profdc9/RFBitBanger/BitBangDisplay/BitBangDisplay-Bottom.png

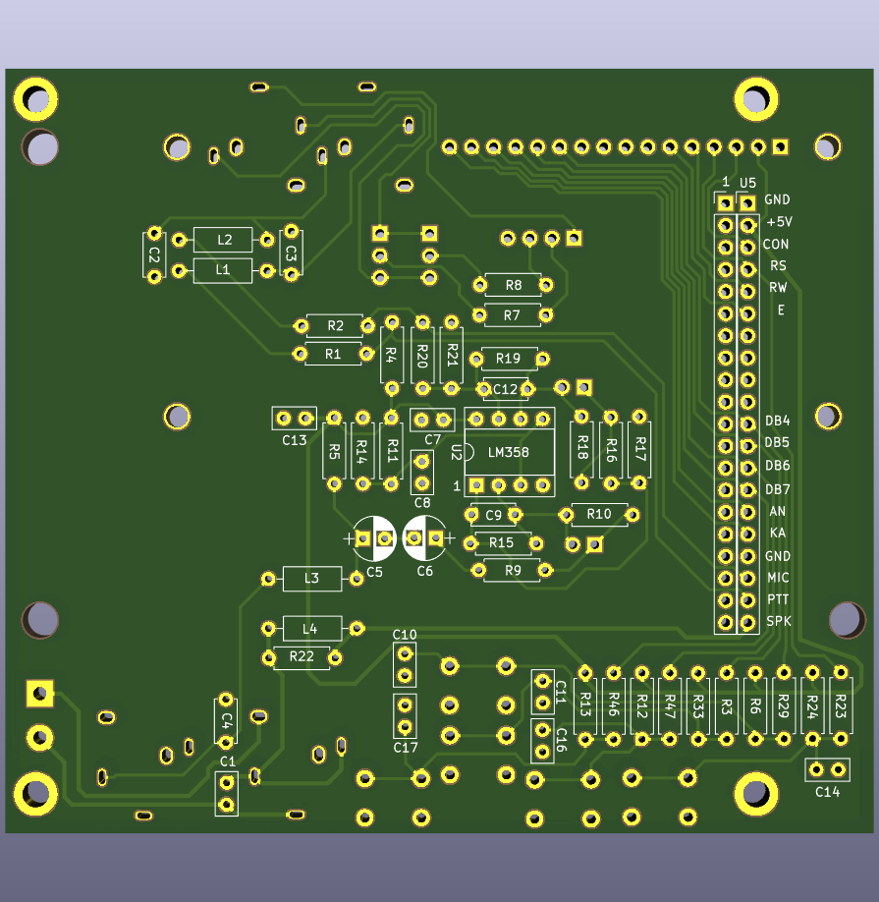
BitBangDisplay/BitBangDisplay-Bottom.png
