profdc9/RFBitBanger/PortableTerminal/PortableTerminal.png

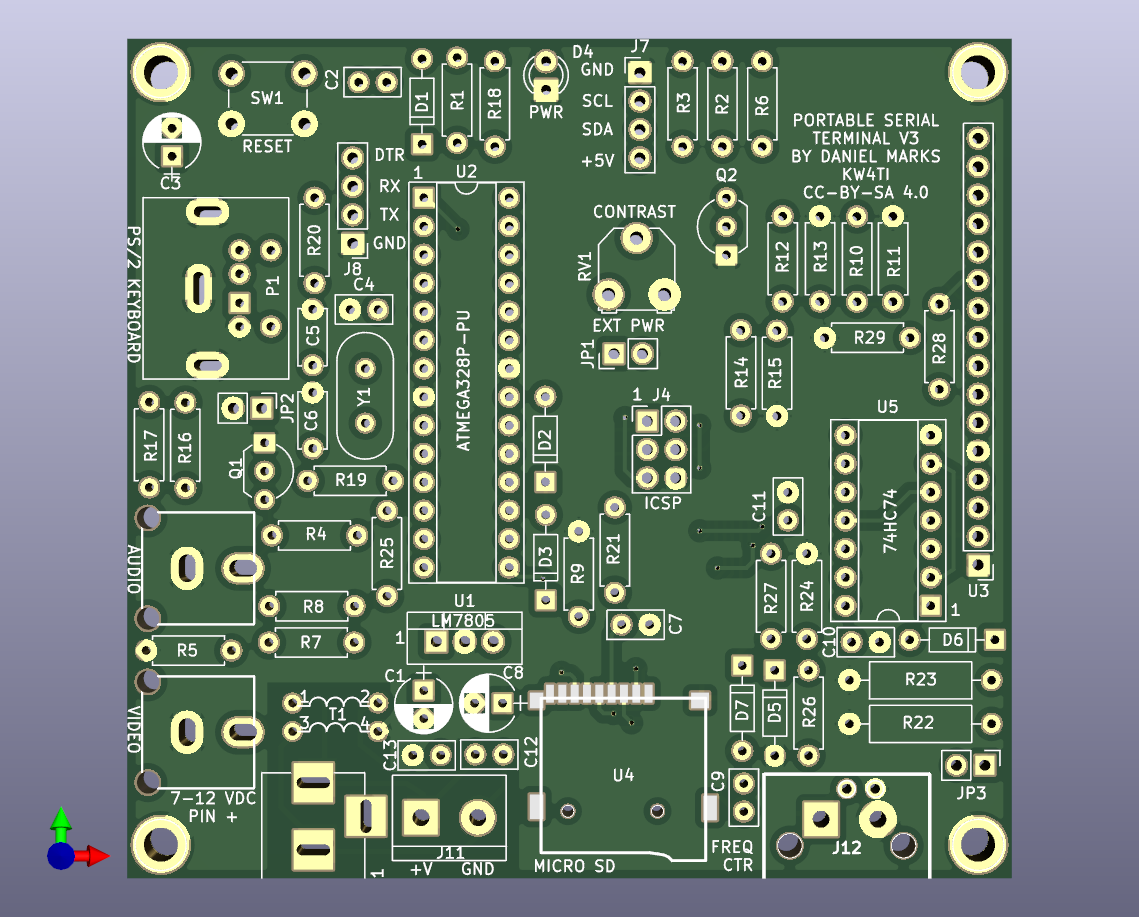
PortableTerminal/PortableTerminal.png
