profdc9/RFBitBanger/RFBitBangerNano/RFBitBangerNano.png

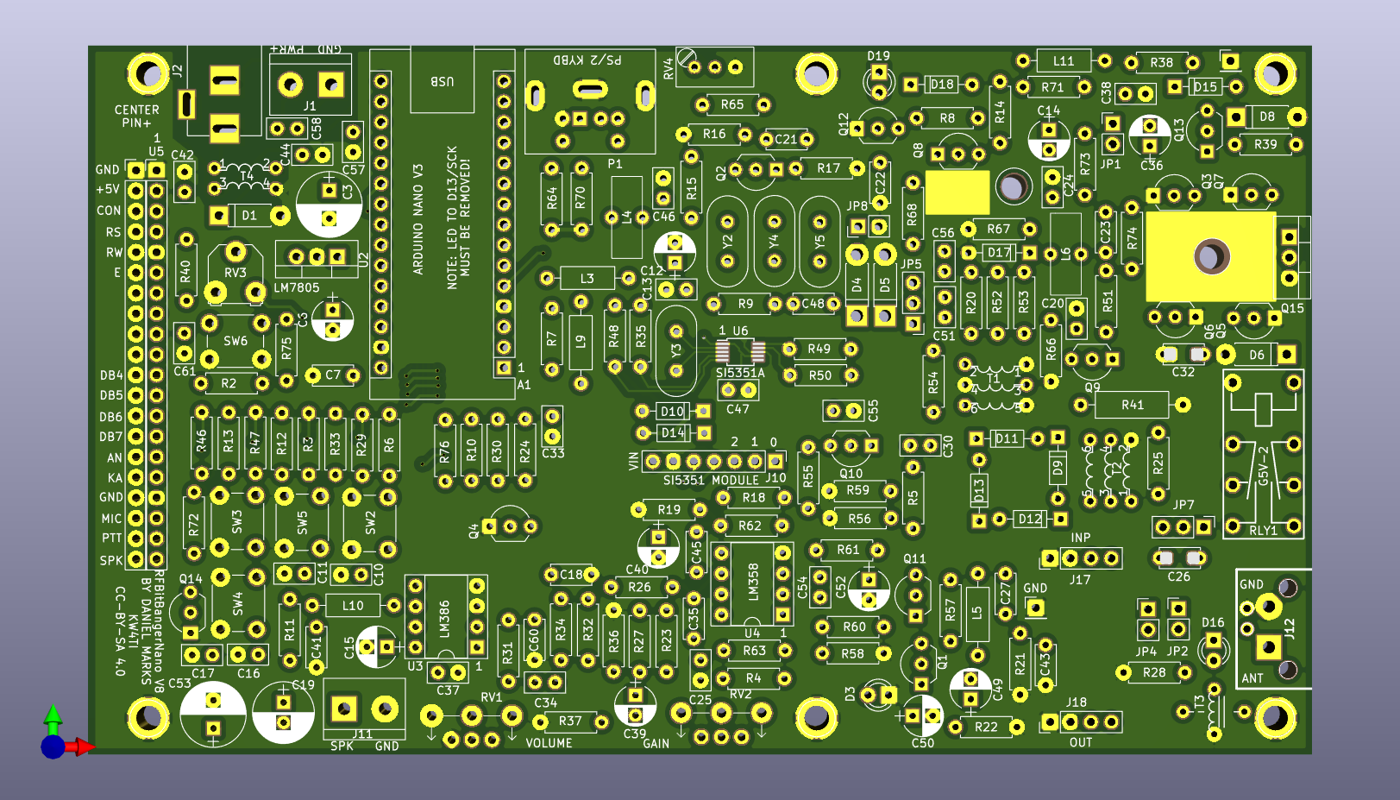
RFBitBangerNano/RFBitBangerNano.png
