profdc9/RFBitBanger/CAD/PaddlesKeyGroundCenter-PaddlesKeyBody.stl

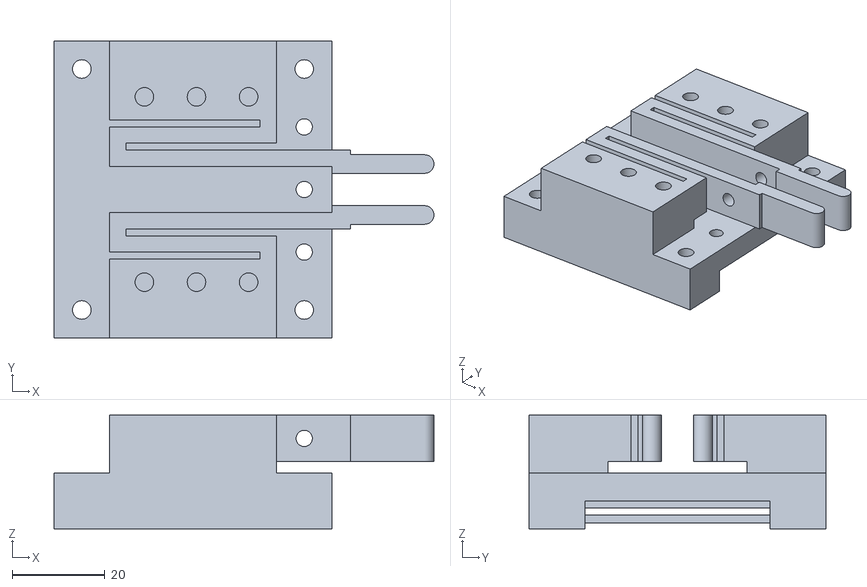
[picture p25: CAD file, 2023-02-17]
CAD/PaddlesKeyGroundCenter-PaddlesKeyBody.stl
82.0 x 64.0 x 24.5
