profdc9/RFBitBanger/CAD/PaddlesKey.FCStd

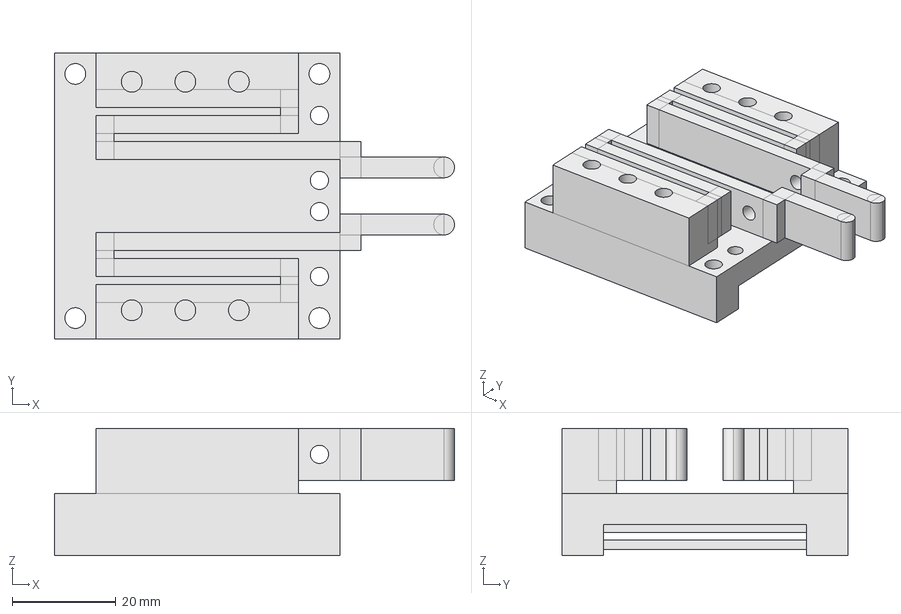
[picture p26: CAD file, 2023-02-17]
CAD/PaddlesKey.FCStd
77.0 x 55.0 x 24.5 mm
