profdc9/RFBitBanger/MatchTester/MatchTester.png

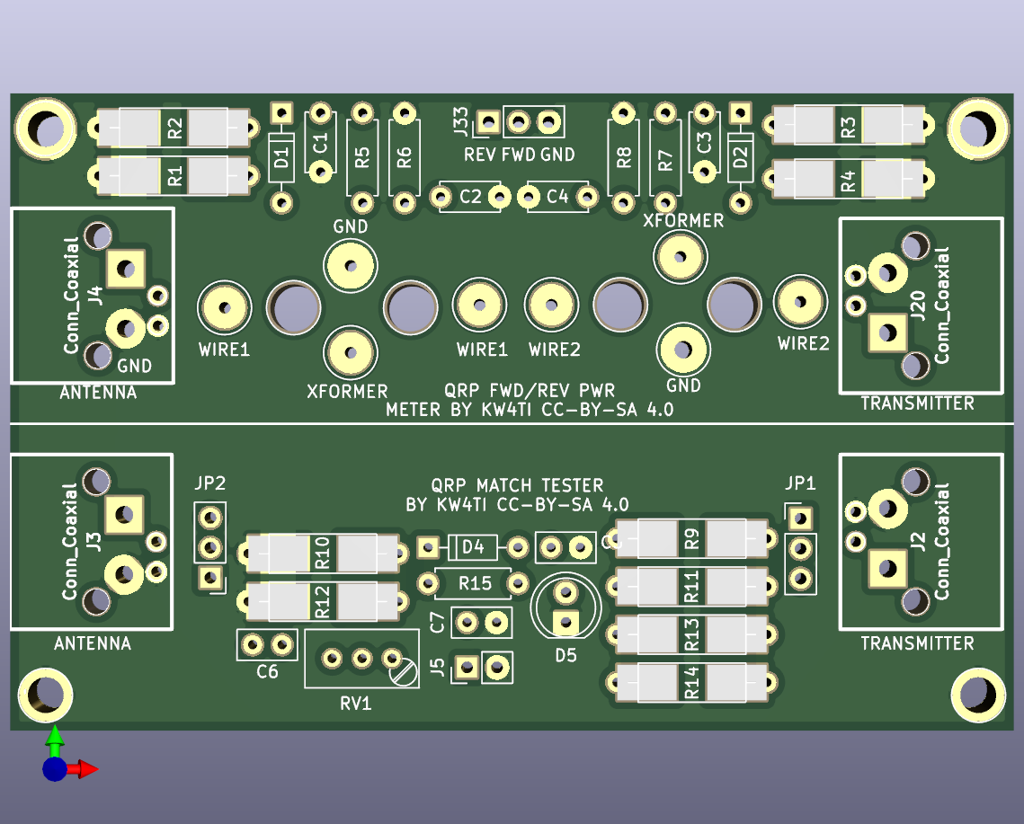
MatchTester/MatchTester.png
