profdc9/RFBitBanger/Code/RFBitBanger/golay.c

/*  golay.c */

/*
 * Copyright (c) 2021 Daniel Marks

This software is provided 'as-is', without any express or implied
warranty. In no event will the authors be held liable for any damages
arising from the use of this software.

Permission is granted to anyone to use this software for any purpose,
including commercial applications, and to alter it and redistribute it
freely, subject to the following restrictions:

1. The origin of this software must not be misrepresented; you must not
   claim that you wrote the original software. If you use this software
   in a product, an acknowledgment in the product documentation would be
   appreciated but is not required.
2. Altered source versions must be plainly marked as such, and must not be
   misrepresented as being the original software.
3. This notice may not be removed or altered from any source distribution.
 */

#ifdef ARDUINO
#include <Arduino.h>
#else
#include "NonArduino.h"
#endif

#include "dspint.h"

#ifdef __cplusplus
extern "C" {
#endif


#undef GOLAY_DEBUG

#ifdef GOLAY_DEBUG
#include <stdio.h>
#include <stdlib.h>
#include <stdint.h>
#endif

#include "golay.h"

const uint16_t PROGMEM golay_matrix[12] =
{
    0b110111000101,
    0b101110001011,
    0b011100010111,
    0b111000101101,
    0b110001011011,
    0b100010110111,
    0b000101101111,
    0b001011011101,
    0b010110111001,
    0b101101110001,
    0b011011100011,
    0b111111111110
};

uint16_t golay_mult(uint16_t wd_enc)
{
   uint16_t enc = 0;
   uint8_t i;
   for (i=12;i>0;)
   {
      i--;
      if (wd_enc & 1) enc ^= pgm_read_word_near(&golay_matrix[i]);
      wd_enc >>= 1;
   }
   return enc;
}

uint32_t golay_encode(uint16_t wd_enc)
{
  uint16_t enc = golay_mult(wd_enc);
  return (((uint32_t)enc) << 12) | wd_enc;
}

uint16_t golay_decode(uint32_t codeword, uint8_t *biterrs)
{
  uint16_t enc = codeword & 0xFFF;
  uint16_t parity = codeword >> 12;
  uint8_t i, biterr;
  uint16_t syndrome, parity_syndrome;

  /* if there are three or fewer errors in the parity bits, then
     we hope that there are no errors in the data bits, otherwise
     the error is uncorrected */
  syndrome = golay_mult(enc) ^ parity;
  biterr = hamming_weight_16(syndrome);
  if (biterr <= 3)
  {
     *biterrs = biterr;
     return enc;
  }

  /* check to see if the parity bits have no errors */
  parity_syndrome = golay_mult(parity) ^ enc;
  biterr = hamming_weight_16(parity_syndrome);
  if (biterr <= 3)
  {
     *biterrs = biterr;
     return enc ^ parity_syndrome;
  }

  /* we flip each bit of the data to see if we have two or fewer errors */
  for (i=12;i>0;)
  {
      i--;
      biterr = hamming_weight_16(syndrome ^ pgm_read_word_near(&golay_matrix[i]));
      if (biterr <= 2)
      {
          *biterrs = biterr+1;
          return enc ^ (((uint16_t)0x800) >> i);
      }
  }

  /* we flip each bit of the parity to see if we have two or fewer errors */
  for (i=12;i>0;)
  {
      i--;
      uint16_t par_bit_synd = parity_syndrome ^ pgm_read_word_near(&golay_matrix[i]);
      biterr = hamming_weight_16(par_bit_synd);
      if (biterr <= 2)
      {
          *biterrs = biterr+1;
          return enc ^ par_bit_synd;
      }
  }
  return 0xFFFF;   /* uncorrectable error */
}

#ifdef GOLAY_DEBUG

uint8_t golay_hamming_weight_24(uint32_t n)
{
  uint8_t s = 0, v;
  v = (n >> 16) & 0xFF;
  while (v)
  {
      v = v & (v - 1);
      s++;
  }
  v = (n >> 8) & 0xFF;
  while (v)
  {
      v = v & (v - 1);
      s++;
  }
  v = n & 0xFF;
  while (v)
  {
      v = v & (v - 1);
      s++;
  }
  return s;
}

uint8_t count_reversals(uint32_t n)
{
  uint8_t i,j,k,rev,mrev=0;
  for (i=0;i<3;i++)
  {
    rev = 0;
    for (j=i;j<23;j+=4)
    {
       if (((n >> j) & 0x01) != ((n >> (j+1)) & 0x01))
            rev++;
    }
    if (rev>mrev) mrev=rev;
  }
  return mrev;
}

void generate_random_permutation(uint8_t num_bits, uint8_t bitlist[])
{
    uint8_t i=0,j;
    while (i<num_bits)
    {
        uint8_t p = rand() % num_bits;
        for (j=0;j<i;j++)
            if (bitlist[j] == p) continue;
        bitlist[i++] = p;
    }
}

uint32_t golay_unpermute_bits(uint32_t bits, uint8_t num_bits, uint8_t bitlist[])
{
   uint8_t i;
   uint32_t pb = 0;
   for (i=0;i<num_bits++;i++)
        if (bits & (1 << bitlist[i]))
            pb |= (1 << i);
   return pb;
}

uint32_t golay_permute_bits(uint32_t bits, uint8_t num_bits, uint8_t bitlist[])
{
   uint8_t i;
   uint32_t pb = 0;
   for (i=0;i<num_bits++;i++)
        if (bits & (1 << i))
            pb |= (1 << bitlist[i]);
   return pb;
}

void test_all_codes(void)
{
    uint32_t xorval;
    uint16_t c = 0;
    uint32_t tmaxminrev = 0, minwt24 = 3000;
    uint8_t permutation[32],i;

    for (xorval=0x1000000;xorval>0;)
    {
        --xorval;
        uint8_t wt24 = golay_hamming_weight_24(xorval);
        //generate_random_permutation(24,permutation);
        uint16_t min_rev = 100, max_rev = 0;
        for (c=0;c<0x1000;c++)
        {
            uint32_t m = golay_encode(c) ^ xorval;
            //m = golay_permute_bits(m,24,permutation);
            uint8_t revs = count_reversals(m);
            if (min_rev>revs) min_rev = revs;
            if (max_rev<revs) max_rev = revs;
        }
        if ((tmaxminrev <= min_rev) && (wt24 <= minwt24))
        {
            tmaxminrev = min_rev;
            minwt24 = wt24;
            printf("xorval=%06X wt=%02d min_rev=%d max_rev=%d\n",xorval,wt24,min_rev,max_rev);
            //printf("permutation: ");
            //for (i=0;i<24;i++)
            //    printf("%d%c",permutation[i], i == 23 ? '\n' : ',');
        }
    }
}

void print_binary(uint32_t n, uint8_t d)
{
  uint8_t i;
  for (i=d;i>0;)
  {
    printf( (n & (1 << (--i))) ? "1" : "0");
    if (i>0) printf(",");
  }
}

uint32_t generate_n_errors(uint8_t n)
{
  uint32_t d = 0;
  while (n>0)
  {
    uint32_t bitmask = 1u << (rand() % 24);
    if (!(d & bitmask))
    {
        d |= bitmask;
        n--;
    }
  }
  return d;
}

void test_decode(void)
{
    uint8_t i, biterrs;
    char s[100];
    for (i=0;i<100;i++)
    {
    uint16_t input = rand() & 0xFFF;
    printf("input:   ");
    print_binary(input,12);
    uint32_t enc = golay_encode(input);
    printf("\nencoded: ");
    print_binary(enc,24);
    uint16_t wd = golay_mult(enc >> 12);
    printf("\nmult:    ");
    print_binary(wd,12);
    uint32_t errors = generate_n_errors(3);
    printf("\nerrors:  ");
    print_binary(errors,24);
    enc ^= errors;
    printf("\nencerr:  ");
    print_binary(enc,24);
    uint16_t dec = golay_decode(enc,&biterrs);
    printf("\ndecode:  ");
    print_binary(dec,12);
    printf(" %d\n",biterrs);
    if (dec != input)
        printf("\n!!!!!!!!!!!!!!!!!\n");
    gets(s);
    }
}

void main(void)
{
    srand(111);
    test_decode();
    //test_all_codes();
}
#endif
