profdc9/RFBitBanger/Code/RFBitBanger/si5351simple.cpp

/* si5351simple.cpp

*/

/*
   Copyright (c) 2021 Daniel Marks

  This software is provided 'as-is', without any express or implied
  warranty. In no event will the authors be held liable for any damages
  arising from the use of this software.

  Permission is granted to anyone to use this software for any purpose,
  including commercial applications, and to alter it and redistribute it
  freely, subject to the following restrictions:

  1. The origin of this software must not be misrepresented; you must not
   claim that you wrote the original software. If you use this software
   in a product, an acknowledgment in the product documentation would be
   appreciated but is not required.
  2. Altered source versions must be plainly marked as such, and must not be
   misrepresented as being the original software.
  3. This notice may not be removed or altered from any source distribution.
*/

// This is cobbled together from many sources

#include "si5351simple.h"

#include <stdio.h>
#include <string.h>
#include <inttypes.h>
#include "Arduino.h"

struct _si5351_cached_regs c_regs;

#ifdef SSB_SUPPORT
#define TWI_FAST
#endif

#define TWI_HARDWARE

#ifdef TWI_HARDWARE
void twi_init(void)
{
    TWSR = 0x00;
#ifdef TWI_FAST
    TWBR = 0x02;
#else
    TWBR = 0x0C;
#endif
    TWCR = (1<<TWEN);
}

void twi_start(void)
{
    TWCR = (1<<TWINT)|(1<<TWSTA)|(1<<TWEN);
    while ((TWCR & (1<<TWINT)) == 0);
}

void twi_stop(void)
{
    TWCR = (1<<TWINT)|(1<<TWSTO)|(1<<TWEN);
}

void twi_write(uint8_t u8data)
{
	  TWDR = u8data;
    TWCR = (1<<TWINT)|(1<<TWEN);
    while ((TWCR & (1<<TWINT)) == 0);
}

void si5351_write(uint8_t reg_addr, uint8_t reg_value)
{
   twi_start();
   twi_write(SI5351_ADDRESS << 1);
   twi_write(reg_addr);
   twi_write(reg_value);
   twi_stop();
} 

void si5351_write_mult(uint8_t reg_addr, uint8_t num, uint8_t reg_value[])
{
   twi_start();
   twi_write(SI5351_ADDRESS << 1);
   twi_write(reg_addr);
   for (uint8_t i=0;i<num;i++)
       twi_write(reg_value[i]);
   twi_stop();
} 

#else
#include <Wire.h>
void twi_init(void)
{
  Wire.begin();                    
}

void si5351_write(uint8_t regist, uint8_t value)
{
  Wire.beginTransmission(SI5351_ADDRESS);                      
  Wire.write(regist);                        
  Wire.write(value);                                
  Wire.endTransmission();                           
}
#endif

si5351simple::si5351simple(uint8_t p_cap, uint32_t p_xo_freq)
{
  twi_init();
  cap = p_cap;
  xo_freq = p_xo_freq;
}

void si5351simple::set_xo_freq(uint32_t p_xo_freq)
{
  xo_freq = p_xo_freq;
}

uint32_t si5351simple::get_xo_freq(void)
{
  return xo_freq;
}

void si5351simple::set_offset_fast(int16_t offset)
{
  uint16_t a;
  int32_t b;
  uint32_t P1, P2;

  a = c_regs.a;
  if (offset > 0)
    b = c_regs.b + ((uint32_t)(offset)) * c_regs.b_offset /  SI5351_FREQ_OFFSET;
  else
    b = c_regs.b - ((uint32_t)(-offset)) * c_regs.b_offset /  SI5351_FREQ_OFFSET;

  if (b < 0)
  {
    a--;
    b += FEEDBACK_MULTIPLIER_C;
  } else if (b > FEEDBACK_MULTIPLIER_C)
  {
    a++;
    b -= FEEDBACK_MULTIPLIER_C;
  }
  
  P2 = b >> (FEEDBACK_MULTIPLIER_SHIFT-7);
  P1 = (a << 7) + P2 - 512;
  P2 = (b << 7) - (P2 << FEEDBACK_MULTIPLIER_SHIFT);

  twi_start();
  twi_write(SI5351_ADDRESS << 1);
  twi_write(SI5351_SYNTH_PLL_A + 3);
  twi_write((P1 >> 8) & 0xFF);
  twi_write(P1 & 0xFF);
  twi_write(((uint8_t)(FEEDBACK_MULTIPLIER_C >> 12) & 0xF0) | ((uint8_t)(P2 >> 16) & 0x0F));
  twi_write((P2 >> 8) & 0xFF);
  twi_write(P2 & 0xFF);
  twi_stop();
  
#ifndef TWI_FAST 
#warning "TWI FAST Required!!!!!! 1k pullups required on SDA/SCL"
#endif
}

void si5351simple::set_registers(uint8_t synth_no, si5351_synth_regs *s_regs, 
								 uint8_t multisynth_no, si5351_multisynth_regs *m_regs)
{
   uint8_t synth_base = 0xFF, multisynth_base = 0xFF, i;
   switch (multisynth_no)
   {
	   case 0: multisynth_base = SI5351_MULTISYNTH_0; break;
	   case 1: multisynth_base = SI5351_MULTISYNTH_1; break;
	   case 2: multisynth_base = SI5351_MULTISYNTH_2; break;
   }
   if (multisynth_base == 0xFF) return;
   switch (synth_no)
   {
	   case 0: synth_base = SI5351_SYNTH_PLL_A; break;
	   case 1: synth_base = SI5351_SYNTH_PLL_B; break;
   }

   setSourceAndPower(multisynth_no, 0, 0, 0, 0, 0);
   if (s_regs != NULL)
   {
	   for (i=0;i<8;i++) si5351_write(synth_base+i, s_regs->regs[i]);
   }
   for (i=0;i<8;i++) si5351_write(multisynth_base+i, m_regs->regs[i]);
   si5351_write(multisynth_no+165, m_regs->offset);
	   
   setSourceAndPower(multisynth_no, m_regs->offset != 0, 1, synth_no, 3, m_regs->inv);
   if (synth_base != 0xFF)
      si5351_write(177, synth_no ? 0x80 : 0x20);
}									 

static void calc_multisynth_registers(uint8_t regs[], uint8_t R, uint32_t a, uint32_t b)
{
  uint32_t P1, P2;

  P2 = b >> (FEEDBACK_MULTIPLIER_SHIFT-7);
  P1 = (a << 7) + P2 - 512;
  P2 = (b << 7) - (P2 << FEEDBACK_MULTIPLIER_SHIFT);
  
  regs[0] = (FEEDBACK_MULTIPLIER_C >> 8) & 0xFF;
  regs[1] = FEEDBACK_MULTIPLIER_C & 0xFF;
  regs[2] = (((uint8_t)(P1 >> 16)) & 0x03) | (R << 4);
  regs[3] = (P1 >> 8) & 0xFF;
  regs[4] = P1 & 0xFF;  
  regs[5] = ((uint8_t)(FEEDBACK_MULTIPLIER_C >> 12) & 0xF0) | ((uint8_t)(P2 >> 16) & 0x0F);
  regs[6] = (P2 >> 8) & 0xFF;
  regs[7] = P2 & 0xFF;
}

#if 0
void si5351simple::print_c_regs(void)
{
  Serial.print("\r\nR=");
  Serial.println(c_regs.R);
  Serial.print("mult_ratio=");
  Serial.println(c_regs.mult_ratio);
  Serial.print("fvco=");
  Serial.println(c_regs.fvco);
  Serial.print("a=");
  Serial.println(c_regs.a);
  Serial.print("b=");
  Serial.println(c_regs.b);
  Serial.print("b_offset_pos=");
  Serial.println(c_regs.b_offset_pos);
  Serial.print("b_offset_neg=");
  Serial.println(c_regs.b_offset_neg);
}
#endif

void si5351simple::calc_registers(uint32_t frequency, uint8_t phase, uint8_t calc_offset, si5351_synth_regs *s_regs, si5351_multisynth_regs *m_regs, si5351_cached_regs *c_regs)
{
  uint8_t R;
  int16_t offset;
  uint16_t mult_ratio;
  uint32_t fvco;

  si5351_cached_regs temp;
  if (c_regs == NULL)
    c_regs = &temp;

  if (phase >= 0x80)
  {
    phase -= 0x80;
    m_regs->inv = 1;
  } else m_regs->inv = 0;

  if (frequency < 5000000)
      mult_ratio = 400000000ul / frequency;
  else if (frequency < 7000000)
      mult_ratio = 550000000ul / frequency;
  else mult_ratio = 850000000ul / frequency;

  R = 0;
  offset = SI5351_FREQ_OFFSET;
  while (mult_ratio > 125)
  {
    mult_ratio >>= 1;
    frequency <<= 1;
    offset <<= 1;
    R++;    
  };

  mult_ratio = (mult_ratio + 1) & ~0x01;
  fvco = frequency * mult_ratio;
  
  c_regs->a = fvco / xo_freq;
  c_regs->b = fvco - xo_freq * c_regs->a;
  c_regs->b = ( ((uint64_t)c_regs->b) << FEEDBACK_MULTIPLIER_SHIFT ) / xo_freq;

  if (calc_offset)
  {
    uint32_t fr_offset = ((uint32_t)offset) * mult_ratio;
    c_regs->b_offset = ( ((uint64_t)fr_offset) << FEEDBACK_MULTIPLIER_SHIFT ) / xo_freq;
  }
  
  if (phase)
     m_regs->offset = (uint8_t)((((uint32_t)mult_ratio)*phase) >> 6) & 0x7F;
  else
     m_regs->offset = 0;

  calc_multisynth_registers(s_regs->regs, 0, c_regs->a, c_regs->b);  
  calc_multisynth_registers(m_regs->regs, R, mult_ratio, 0);
}

// off_on = 0 is off, off_on = 1 is on
// pll_source = 1 is PLLB, pll_source = 0 is PLLA
// power=0 2mA, power=1 4 mA, power=2 6 mA, power=3 8 mA
void si5351simple::setSourceAndPower(uint8_t clock_no, uint8_t frac, uint8_t off_on, uint8_t pll_source, uint8_t power, uint8_t inv)
{                        
  if (power > 3) return;
  si5351_write(clock_no+16, (off_on ? 0 : 0x80) + (frac ? 0 : 0x40) + (pll_source ? 0x20 : 0x00) + (inv ? 0x10 : 0x00) + power + 0x0C);
}

void si5351simple::setOutputOnOffMask(uint8_t new_on_mask)
{
  on_mask = new_on_mask ^ 0xFF;
  si5351_write(3, on_mask);
}

void si5351simple::setOutputOnOff(uint8_t clock_no, uint8_t off_on)
{
  if (off_on) on_mask &= ~(1 << clock_no);
    else on_mask |= (1 << clock_no);
  si5351_write(3, on_mask);
}

void si5351simple::start(void)
{
  si5351_write(24, 0xAA);  // make all outputs high impedance when disabled.
  si5351_write(149, 0);    // disable spread spectrum
  si5351_write(9, 0xFF);   // OEB does not control on
  si5351_write(3, 0xFF);   // all outputs off initially
  on_mask = 0xFF;
    
  switch (cap)
  {
     case 6: si5351_write(183, 0x40); break;
     case 8: si5351_write(183, 0x80); break;
     case 10: si5351_write(183, 0xC0); break;
  }
}
